AnandSeeds/Anand-Seeds-Pachamama/arquitectura_de_software.png

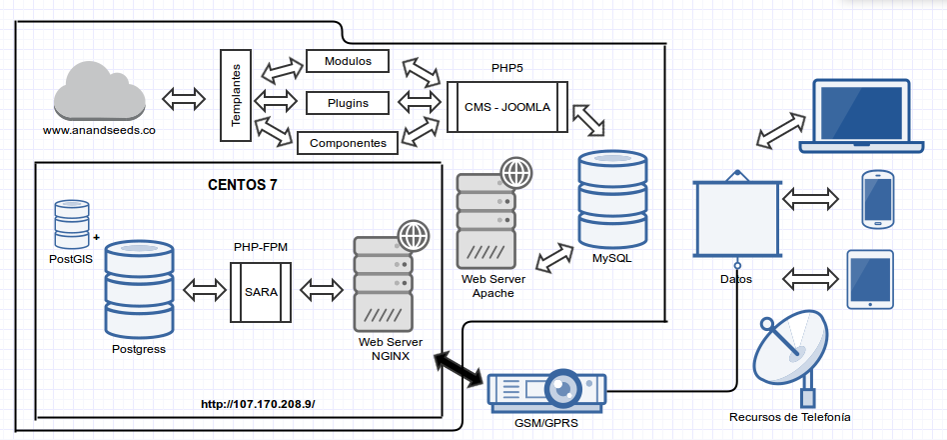
arquitectura_de_software.png
