AnandSeeds/Anand-Seeds-Pachamama/Hardware/Datasheets/500px-UV_index.png

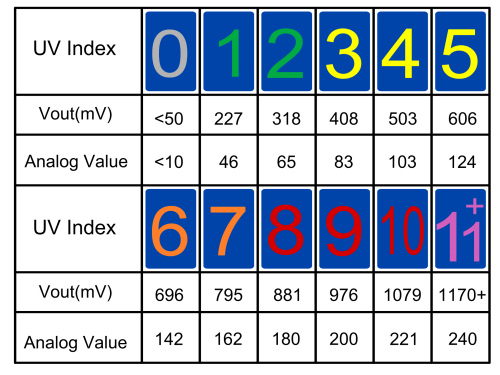
Hardware/Datasheets/500px-UV_index.png
