AnandSeeds/Anand-Seeds-Pachamama/Hardware/Diseños PCB/esquemasFritzing/Esquema.png

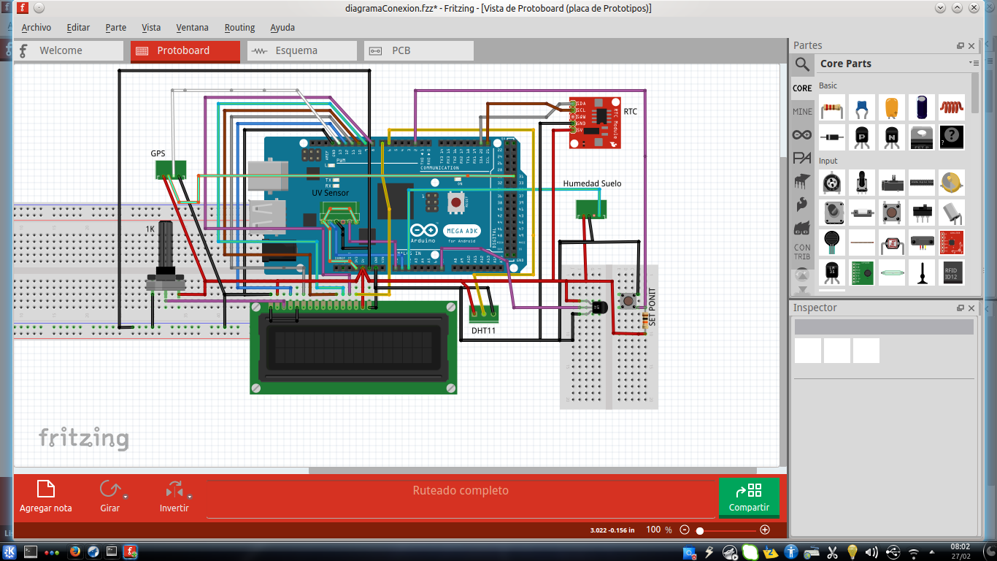
Hardware/Diseños PCB/esquemasFritzing/Esquema.png
