AnandSeeds/Anand-Seeds-Pachamama/SARA/blocks/registros/planDeSiembra/css/img/escudo_oficial_udistrital.png

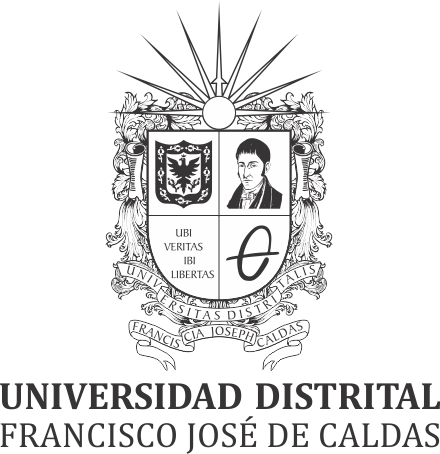
SARA/blocks/registros/planDeSiembra/css/img/escudo_oficial_udistrital.png
