AnandSeeds/Anand-Seeds-Pachamama/SARA/plugin/reportico/css/images/1.jpg

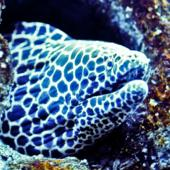
SARA/plugin/reportico/css/images/1.jpg
