AnandSeeds/Anand-Seeds-Pachamama/SARA/plugin/reportico/css/images/2.jpg

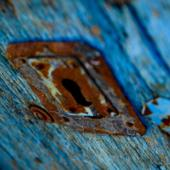
SARA/plugin/reportico/css/images/2.jpg
