AnandSeeds/Anand-Seeds-Pachamama/SARA/plugin/reportico/css/images/3.jpg

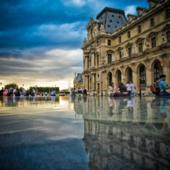
SARA/plugin/reportico/css/images/3.jpg
