AnandSeeds/Anand-Seeds-Pachamama/SARA/plugin/reportico/css/images/4.jpg

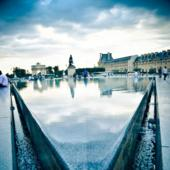
SARA/plugin/reportico/css/images/4.jpg
