AnandSeeds/Anand-Seeds-Pachamama/SARA/plugin/reportico/css/images/5.jpg

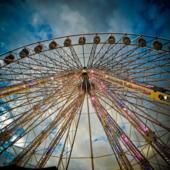
SARA/plugin/reportico/css/images/5.jpg
