AnandSeeds/Anand-Seeds-Pachamama/SARA/plugin/reportico/css/images/6.jpg

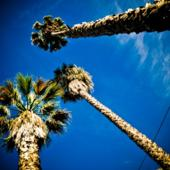
SARA/plugin/reportico/css/images/6.jpg
