AnandSeeds/Anand-Seeds-Pachamama/SARA/plugin/reportico/css/images/bg2.jpg

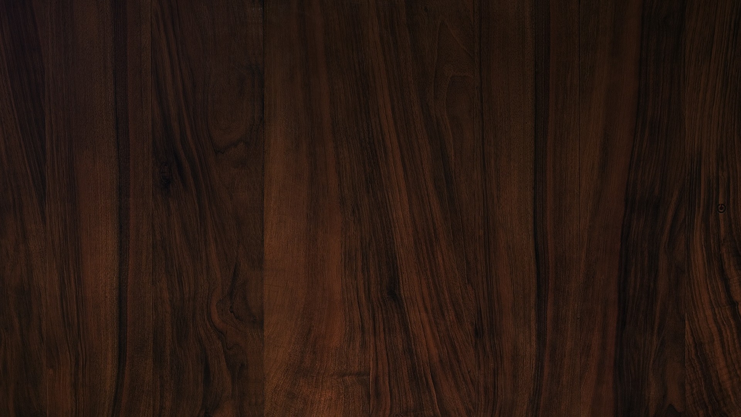
SARA/plugin/reportico/css/images/bg2.jpg
