AnandSeeds/Anand-Seeds-Pachamama/SARA/plugin/reportico/css/images/bg.jpg

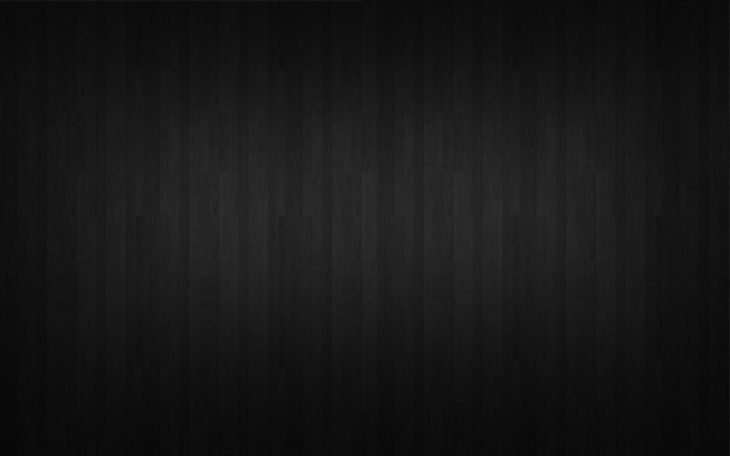
SARA/plugin/reportico/css/images/bg.jpg
