AnandSeeds/Anand-Seeds-Pachamama/SARA/plugin/reportico/css/images/buy.png

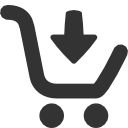
SARA/plugin/reportico/css/images/buy.png
