AnandSeeds/Anand-Seeds-Pachamama/SARA/plugin/reportico/script/reportico/css/edgebotgreen.png

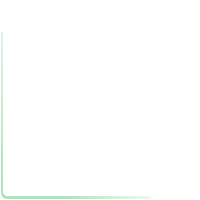
SARA/plugin/reportico/script/reportico/css/edgebotgreen.png
