AnandSeeds/Anand-Seeds-Pachamama/SARA/plugin/reportico/script/reportico/css/edgegreen.png

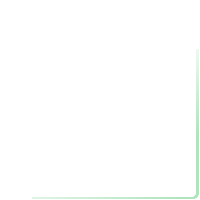
SARA/plugin/reportico/script/reportico/css/edgegreen.png
