AnandSeeds/Anand-Seeds-Pachamama/SARA/plugin/reportico/script/reportico/tcpdf/examples/images/alpha.png

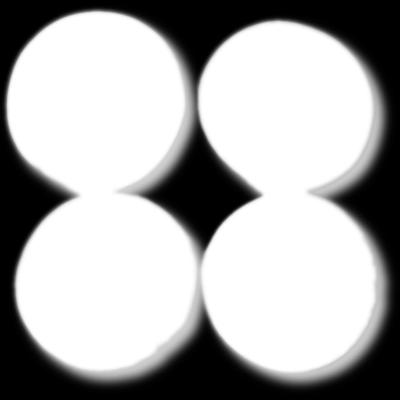
SARA/plugin/reportico/script/reportico/tcpdf/examples/images/alpha.png
