AnandSeeds/Anand-Seeds-Pachamama/SARA/plugin/reportico/script/reportico/tcpdf/examples/images/image_demo.jpg

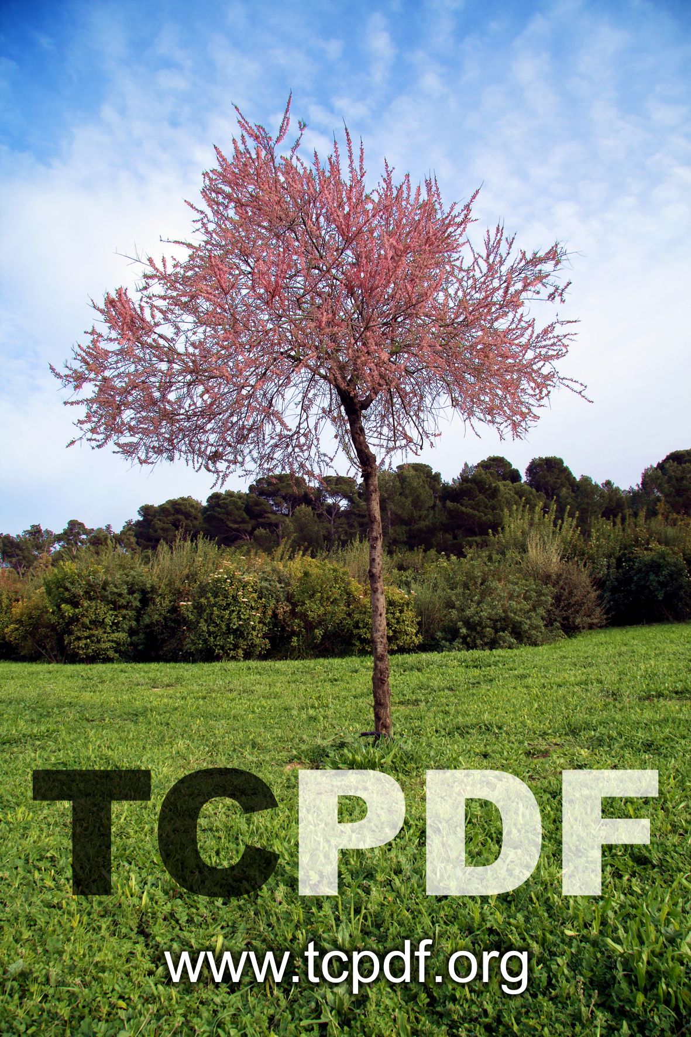
SARA/plugin/reportico/script/reportico/tcpdf/examples/images/image_demo.jpg
