AnandSeeds/Anand-Seeds-Pachamama/SARA/plugin/reportico/script/reportico/tcpdf/examples/images/image_with_alpha.png

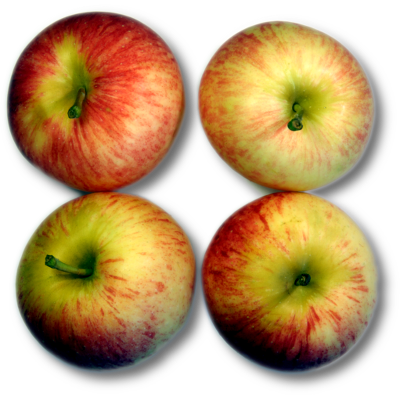
SARA/plugin/reportico/script/reportico/tcpdf/examples/images/image_with_alpha.png
