AnandSeeds/Anand-Seeds-Pachamama/SARA/plugin/reportico/script/reportico/tcpdf/examples/images/tcpdf_cell.png

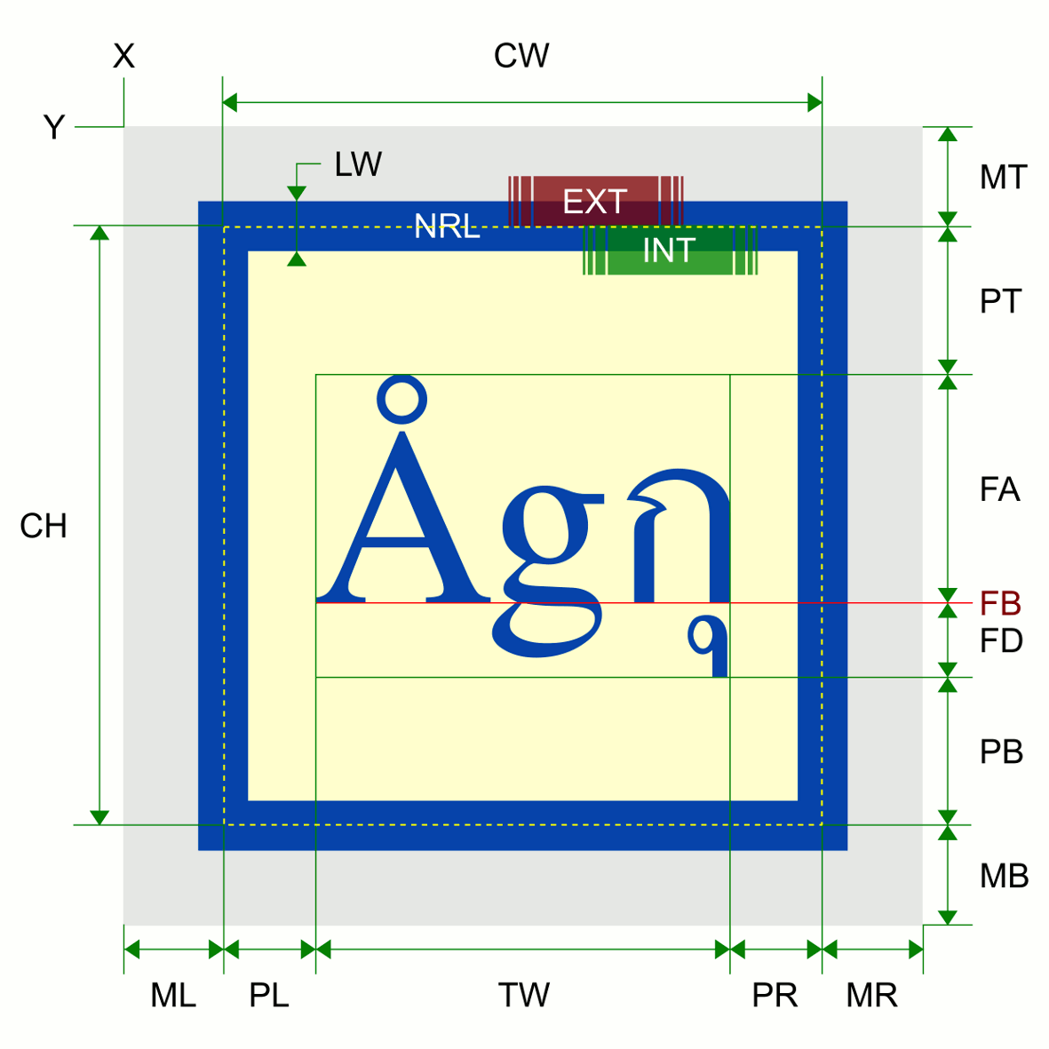
SARA/plugin/reportico/script/reportico/tcpdf/examples/images/tcpdf_cell.png
