AnandSeeds/Anand-Seeds-Pachamama/SARA/plugin/reportico/script/reportico/tcpdf/examples/images/tcpdf_signature.png

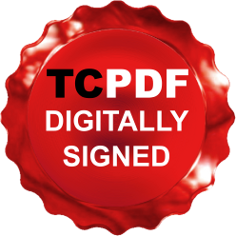
SARA/plugin/reportico/script/reportico/tcpdf/examples/images/tcpdf_signature.png
