AnandSeeds/Anand-Seeds-Pachamama/SARA/blocks/development/saraFormCreator/script/img/tiposComponentes.png

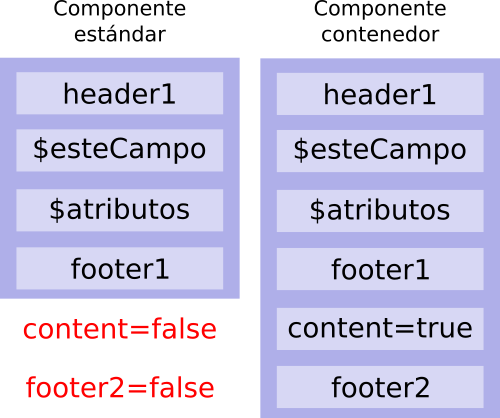
SARA/blocks/development/saraFormCreator/script/img/tiposComponentes.png
